specadmin/Lexus_speedometer/include/potentiometer.h

//-----------------------------------------------------------------------------
#ifndef POTENTIOMETER_H
#define POTENTIOMETER_H
//-----------------------------------------------------------------------------
#include <avr/io.h>
#include "../lib/avr-misc/avr-misc.h"
#include "config.h"
//-----------------------------------------------------------------------------
void set_position(WORD angle);
//-----------------------------------------------------------------------------
#endif
